pondahai/pico_keyboard_ime_terminal/hardware/v2_1/v2_1.kicad_sch

## KiCad design hardware/v2_1/v2_1.kicad_sch (2025-11-12)

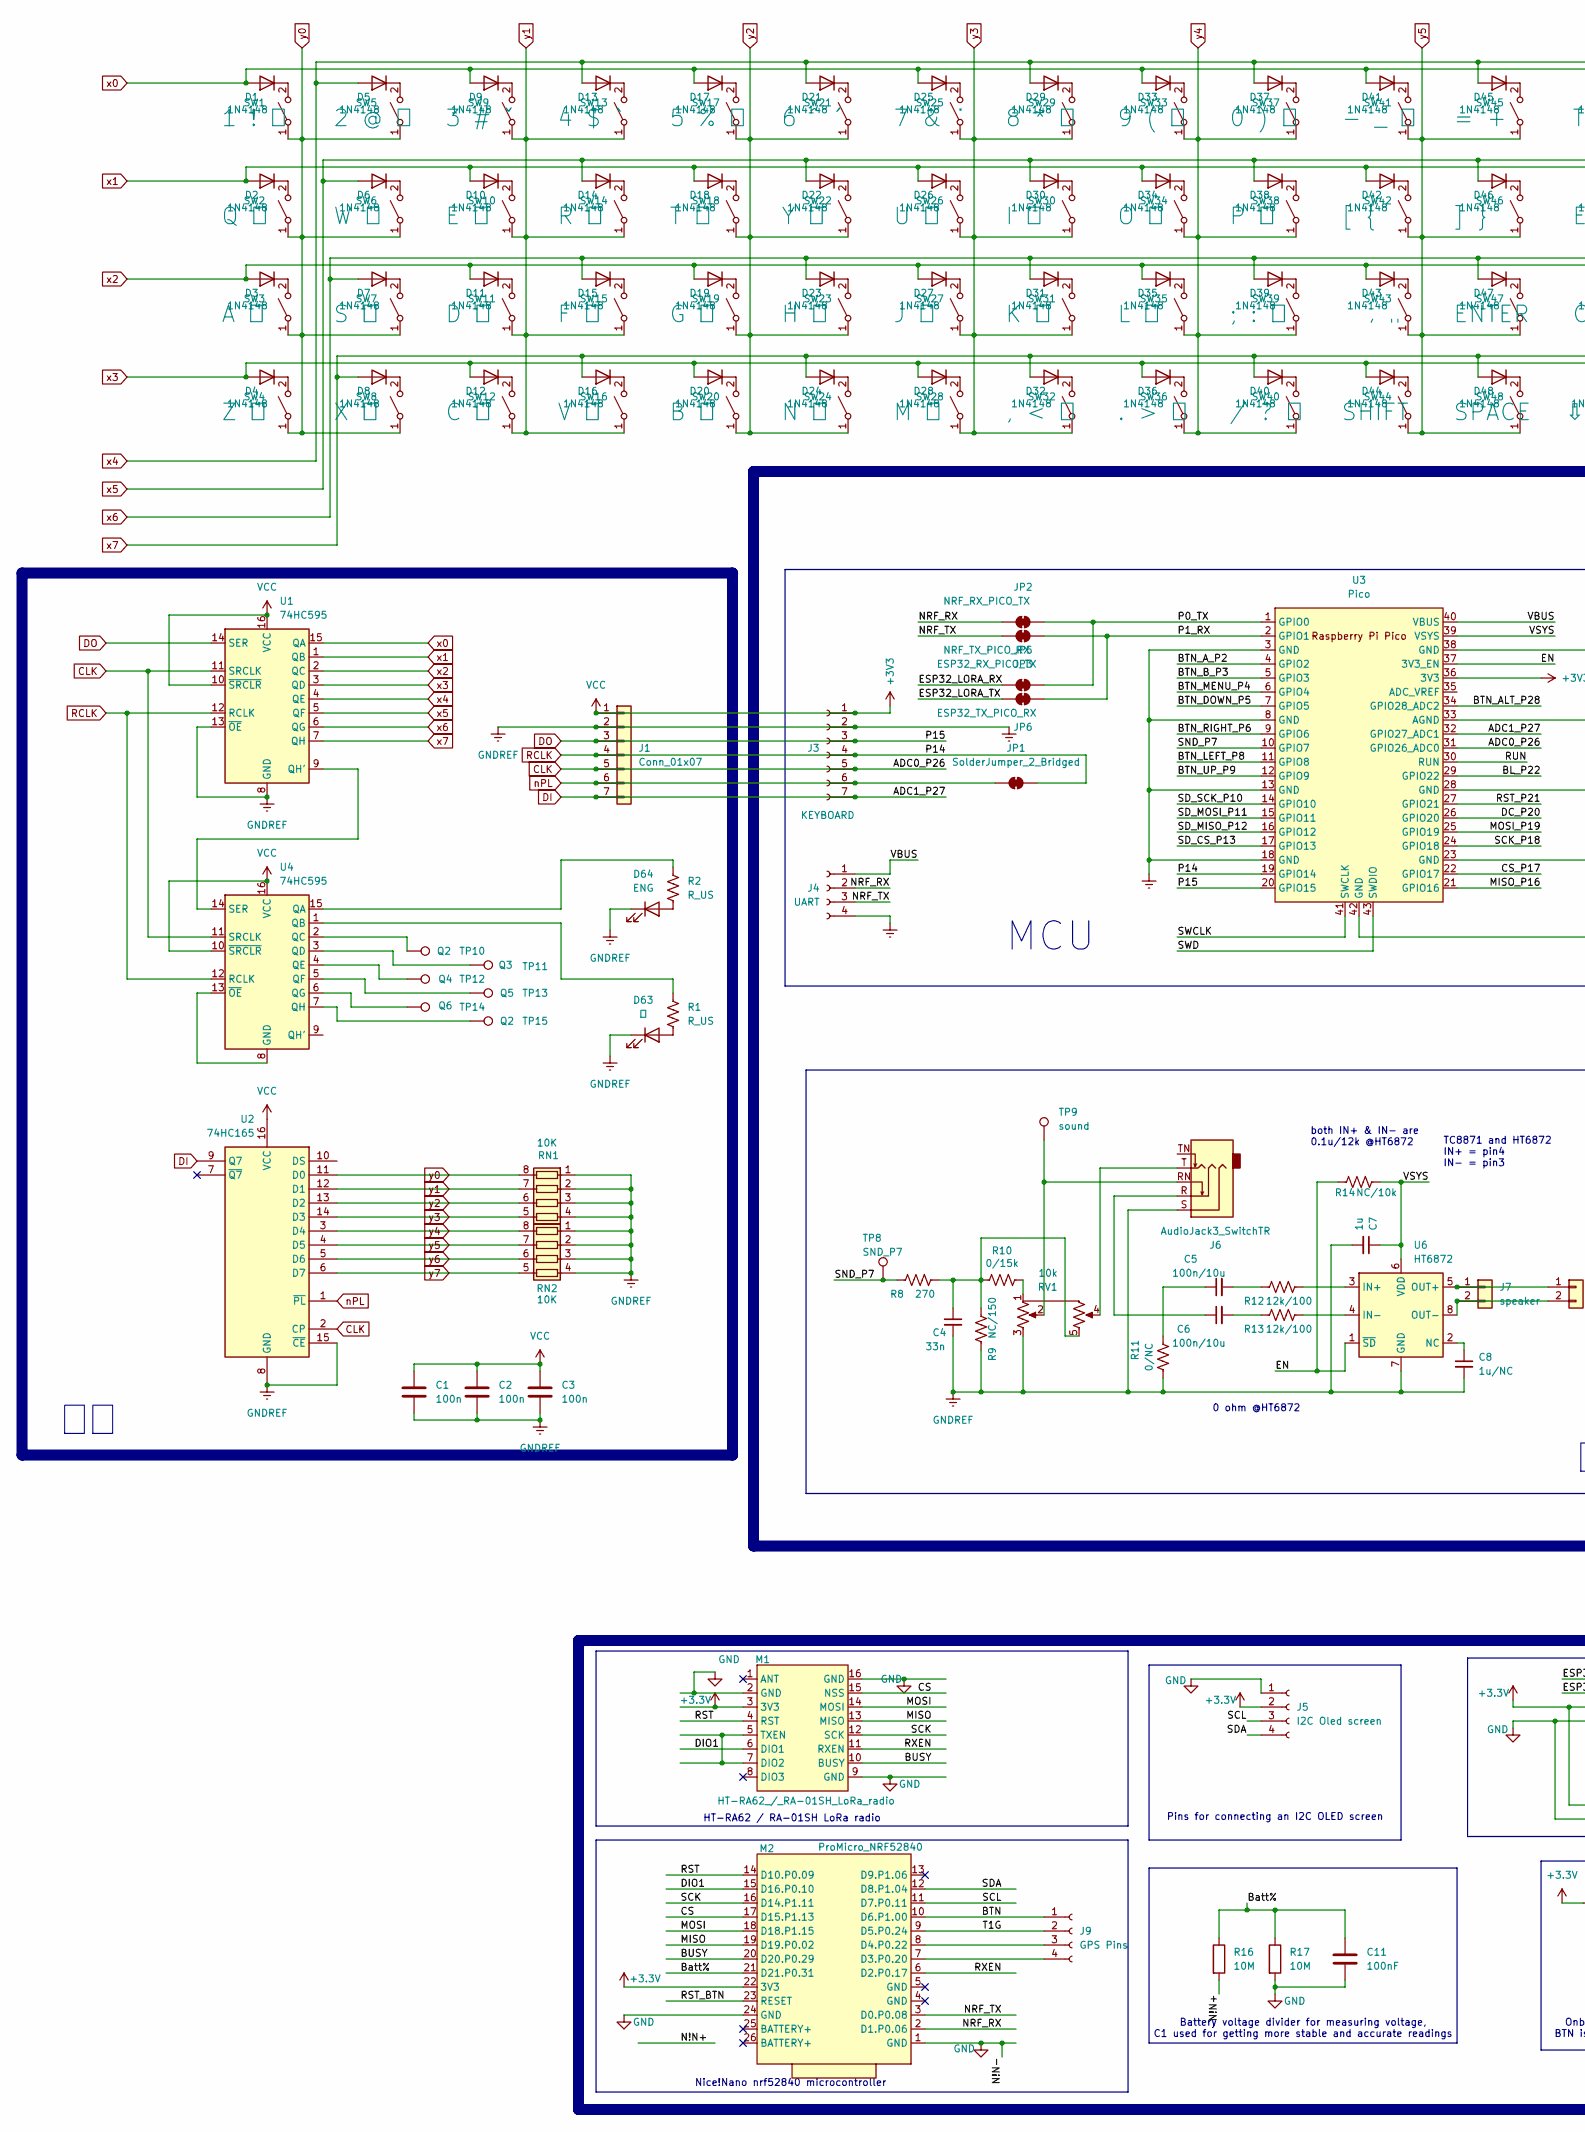
[picture p13: schematic v2_1.kicad_sch, part in row 1, column 1]

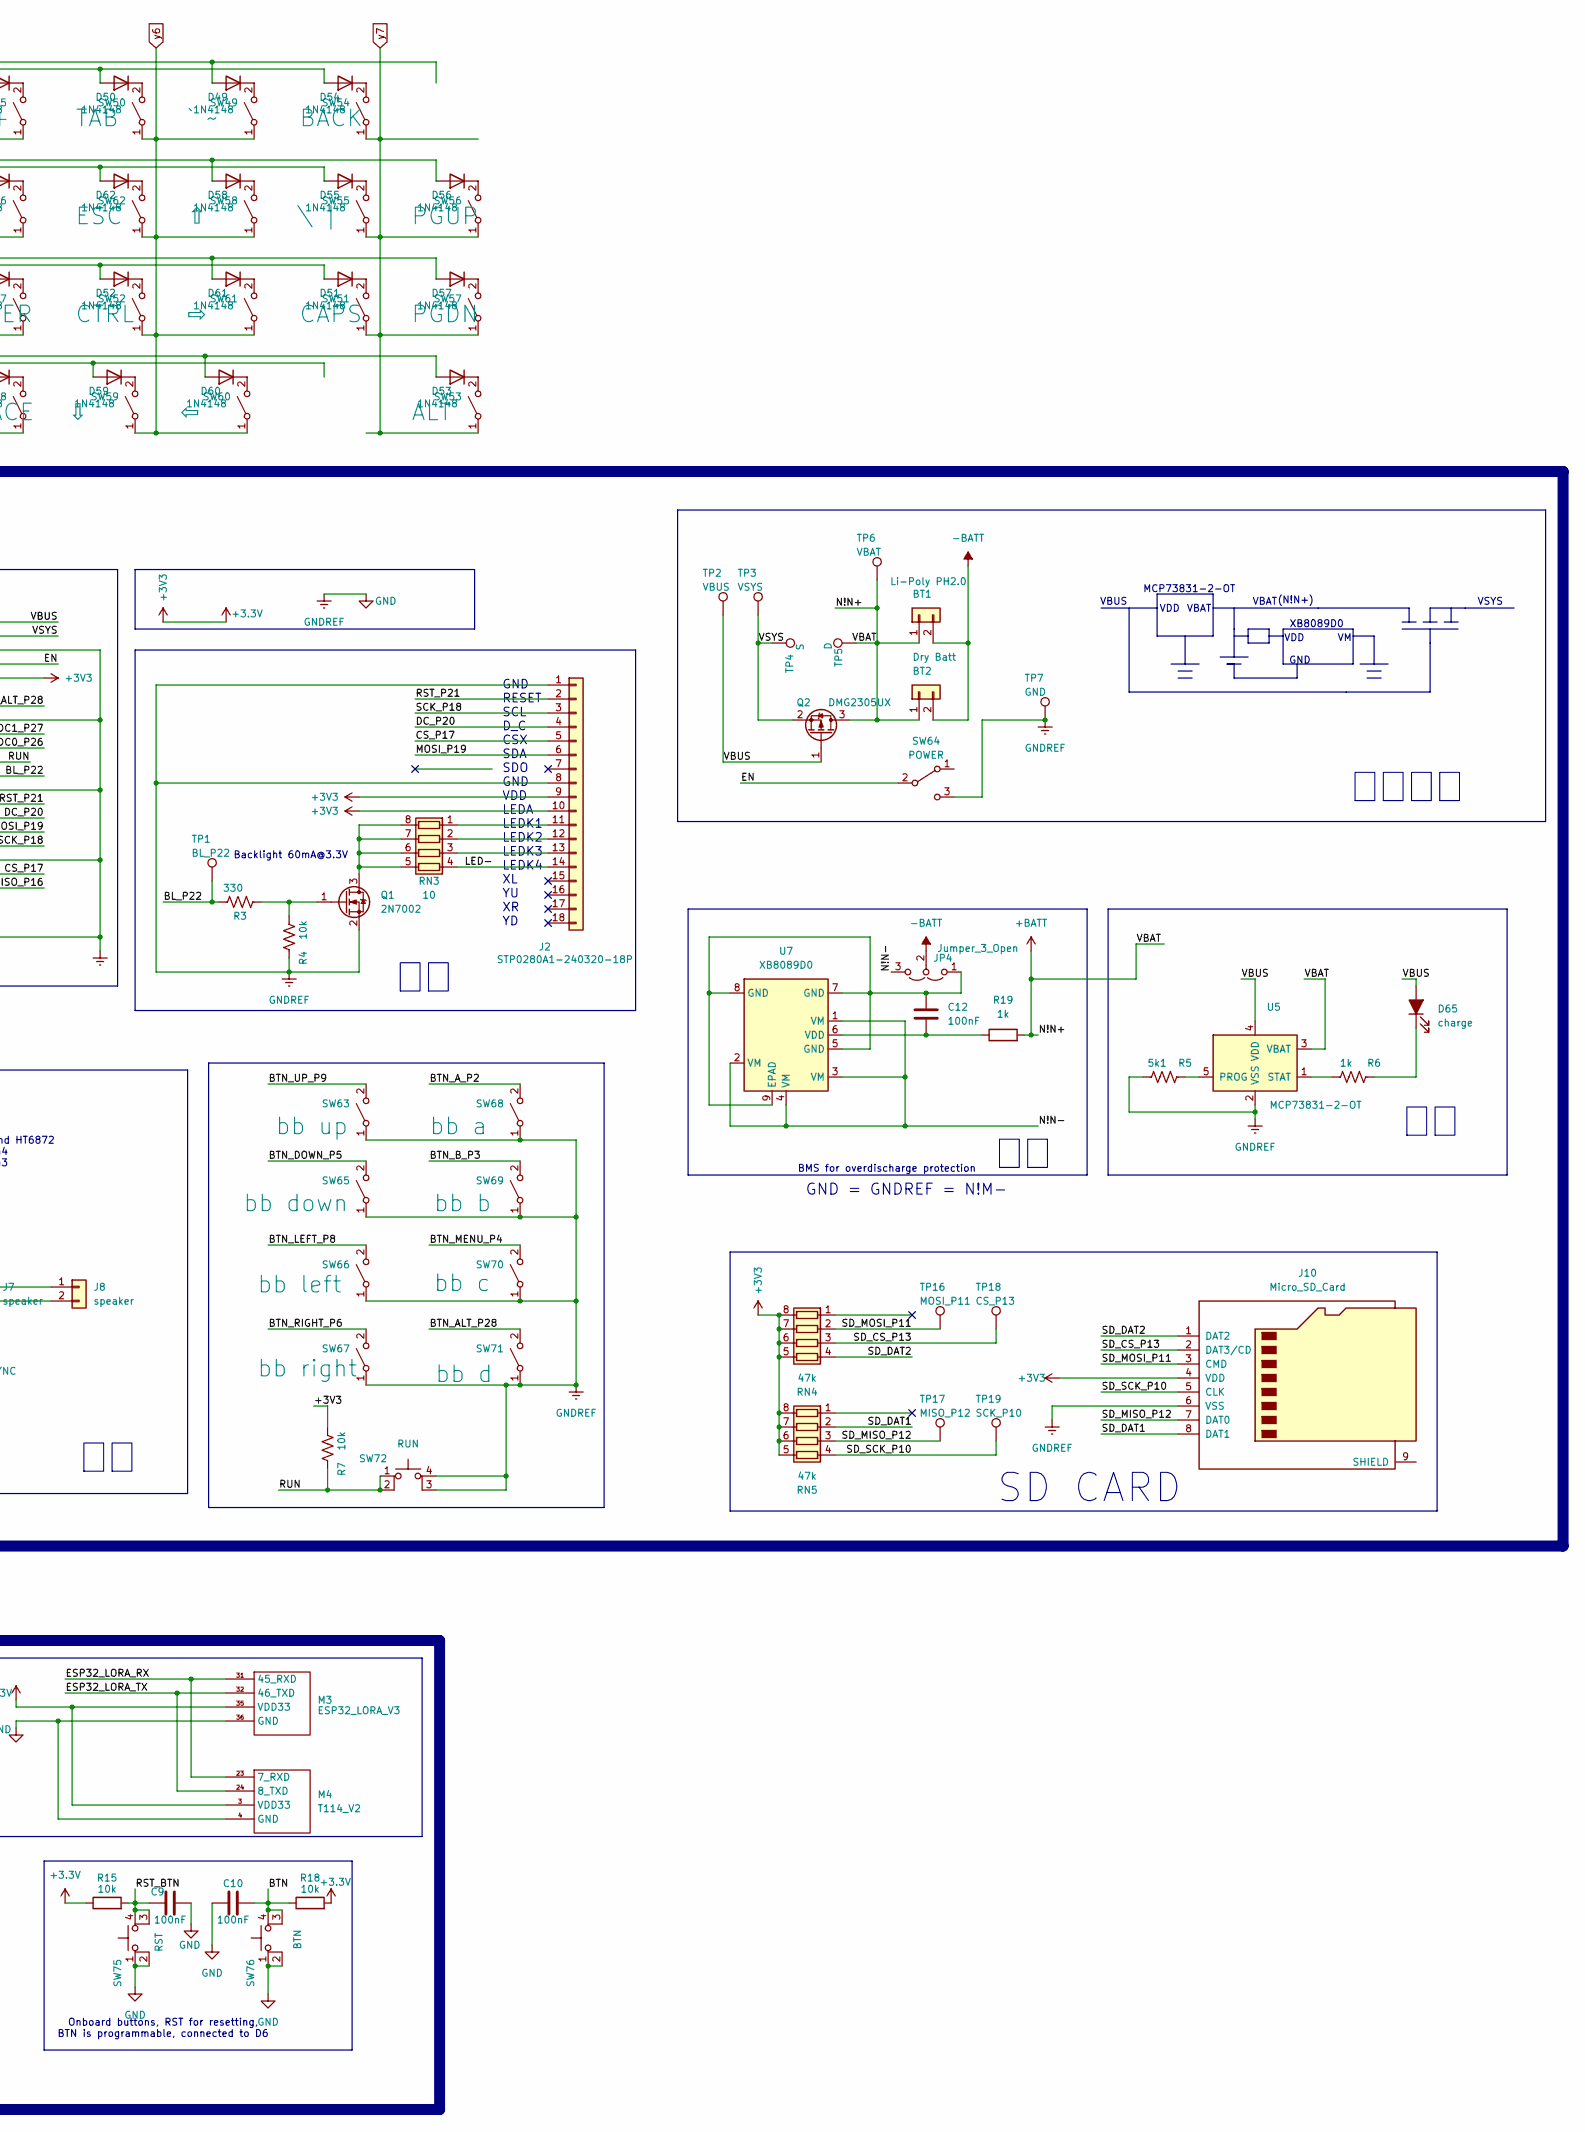
[picture p14: schematic v2_1.kicad_sch, part in row 1, column 2]

Parts:
BT1: Li-Poly PH2.0; JST_PH_B2B-PH-K_1x02_P2.00mm_Vertical
BT2: Dry Batt; BatteryHolder_Keystone_2479_3xAAA
C1, C2, C3: 100n; C_0805_2012Metric_Pad1.18x1.45mm_HandSolder
C4: 33n; C_0805_2012Metric_Pad1.18x1.45mm_HandSolder
C5, C6: 100n/10u; C_0805_2012Metric_Pad1.18x1.45mm_HandSolder
C7: 1u; C_0805_2012Metric_Pad1.18x1.45mm_HandSolder
C8: 1u/NC; C_0805_2012Metric_Pad1.18x1.45mm_HandSolder
C9, C10, C11: 100nF; C_0805_2012Metric_Pad1.18x1.45mm_HandSolder
C12: 100nF; C_1206_3216Metric_Pad1.33x1.80mm_HandSolder
D1, D2, D3, D4, D5, D6, D7, D8, D9, D10, D11, D12, D13, D14, D15, D16, D17, D18, D19, D20, D21, D22, D23, D24, D25, D26, D27, D28, D29, D30, D31, D32, D33, D34, D35, D36, D37, D38, D39, D40, D41, D42, D43, D44, D45, D46, D47, D48, D49, D50, D51, D52, D53, D54, D55, D56, D57, D58, D59, D60, D61, D62: 1N4148; D_0805_JUMPER
D63: ㄅ; LED_D3.0mm_Clear
D64: ENG; LED_D3.0mm_Clear
D65: charge; LED_0805_2012Metric_Pad1.15x1.40mm_HandSolder
J1: Conn_01x07; PinHeader_1x07_P2.54mm_Horizontal
J2: STP0280A1-240320-18P; STP0280A1-240320
J3: KEYBOARD; PinSocket_1x07_P2.54mm_Horizontal
J4: UART; PinSocket_1x04_P2.54mm_Horizontal
J5: I2C Oled screen; PinHeader_1x04_P2.54mm_Vertical
J6: AudioJack3_SwitchTR; audiojack-3.5mm-5p
J7: speaker; SolderWire-0.1sqmm_1x02_P3.6mm_D0.4mm_OD1mm
J8: speaker; Hirose_DF13-02P-1.25DSA_1x02_P1.25mm_Vertical
J9: GPS Pins; PinHeader_1x04_P2.54mm_Vertical
J10: Micro_SD_Card; sd-card
JP1: SolderJumper_2_Bridged; SolderJumper-2_P1.3mm_Bridged_Pad1.0x1.5mm
JP2: NRF_RX_PICO_TX; SolderJumper-2_P1.3mm_Bridged_Pad1.0x1.5mm
JP3: NRF_TX_PICO_RX; SolderJumper-2_P1.3mm_Bridged_Pad1.0x1.5mm
JP4: Jumper_3_Open; SolderJumper-3_P1.3mm_Open_RoundedPad1.0x1.5mm
JP5: ESP32_RX_PICO_TX; SolderJumper-2_P1.3mm_Bridged_Pad1.0x1.5mm
JP6: ESP32_TX_PICO_RX; SolderJumper-2_P1.3mm_Bridged_Pad1.0x1.5mm
M1: HT-RA62_/_RA-01SH_LoRa_radio; HT-RA62 RA-01SH LoRa radio
M2: ProMicro_NRF52840; ProMicro nrf52840
M3: ESP32_LORA_V3; LoRa-ESP32-V3
M4: T114_V2; T114
Q1: 2N7002; SOT-23_Handsoldering
Q2: DMG2305UX; SOT-23_Handsoldering
R1, R2: R_US; R_Axial_DIN0204_L3.6mm_D1.6mm_P7.62mm_Horizontal_0805
R3: 330; R_0805_2012Metric_Pad1.20x1.40mm_HandSolder
R4, R7, R15, R18: 10k; R_0805_2012Metric_Pad1.20x1.40mm_HandSolder
R5: 5k1; R_0805_2012Metric_Pad1.20x1.40mm_HandSolder
R6: 1k; R_0805_2012Metric_Pad1.20x1.40mm_HandSolder
R8: 270; R_0805_2012Metric_Pad1.20x1.40mm_HandSolder
R9: NC/150; R_0805_2012Metric_Pad1.20x1.40mm_HandSolder
R10: 0/15k; R_0805_2012Metric_Pad1.20x1.40mm_HandSolder
R11: 0/NC; R_0805_2012Metric_Pad1.20x1.40mm_HandSolder
R12, R13: 12k/100; R_0805_2012Metric_Pad1.20x1.40mm_HandSolder
R14: NC/10k; R_0805_2012Metric_Pad1.20x1.40mm_HandSolder
R16, R17: 10M; R_0805_2012Metric_Pad1.20x1.40mm_HandSolder
R19: 1k; R_1206_3216Metric_Pad1.30x1.75mm_HandSolder
RN1, RN2: 10K; R_Array_Convex_4x0603
RN3: 10; R_Array_Convex_4x0603
RN4, RN5: 47k; R_Array_Convex_4x0603
RV1: 10k; potentiometre disk 5pin
SW1: 1 ! ㄅ; SW_Push_1P1T_NO_CK_KSC7xxJ
SW2: Q ㄆ; SW_Push_1P1T_NO_CK_KSC7xxJ
SW3: A ㄇ; SW_Push_1P1T_NO_CK_KSC7xxJ
SW4: Z ㄈ; SW_Push_1P1T_NO_CK_KSC7xxJ
SW5: 2 @ ㄉ; SW_Push_1P1T_NO_CK_KSC7xxJ
SW6: W ㄊ; SW_Push_1P1T_NO_CK_KSC7xxJ
SW7: S ㄋ; SW_Push_1P1T_NO_CK_KSC7xxJ
SW8: X ㄌ; SW_Push_1P1T_NO_CK_KSC7xxJ
SW9: 3 # ˇ; SW_Push_1P1T_NO_CK_KSC7xxJ
SW10: E ㄍ; SW_Push_1P1T_NO_CK_KSC7xxJ
SW11: D ㄎ; SW_Push_1P1T_NO_CK_KSC7xxJ
SW12: C ㄏ; SW_Push_1P1T_NO_CK_KSC7xxJ
SW13: 4 $ ˋ; SW_Push_1P1T_NO_CK_KSC7xxJ
SW14: R ㄐ; SW_Push_1P1T_NO_CK_KSC7xxJ
SW15: F ㄑ; SW_Push_1P1T_NO_CK_KSC7xxJ
SW16: V ㄒ; SW_Push_1P1T_NO_CK_KSC7xxJ
SW17: 5 % ㄓ; SW_Push_1P1T_NO_CK_KSC7xxJ
SW18: T ㄔ; SW_Push_1P1T_NO_CK_KSC7xxJ
SW19: G ㄕ; SW_Push_1P1T_NO_CK_KSC7xxJ
SW20: B ㄖ; SW_Push_1P1T_NO_CK_KSC7xxJ
SW21: 6 ^ ˊ; SW_Push_1P1T_NO_CK_KSC7xxJ
SW22: Y ㄗ; SW_Push_1P1T_NO_CK_KSC7xxJ
SW23: H ㄘ; SW_Push_1P1T_NO_CK_KSC7xxJ
SW24: N ㄙ; SW_Push_1P1T_NO_CK_KSC7xxJ
SW25: 7 & ˙; SW_Push_1P1T_NO_CK_KSC7xxJ
SW26: U ㄧ; SW_Push_1P1T_NO_CK_KSC7xxJ
SW27: J ㄨ; SW_Push_1P1T_NO_CK_KSC7xxJ
SW28: M ㄩ; SW_Push_1P1T_NO_CK_KSC7xxJ
SW29: 8 * ㄚ; SW_Push_1P1T_NO_CK_KSC7xxJ
SW30: I ㄛ; SW_Push_1P1T_NO_CK_KSC7xxJ
SW31: K ㄜ; SW_Push_1P1T_NO_CK_KSC7xxJ
SW32: , < ㄝ; SW_Push_1P1T_NO_CK_KSC7xxJ
SW33: 9 ( ㄞ; SW_Push_1P1T_NO_CK_KSC7xxJ
SW34: O ㄟ; SW_Push_1P1T_NO_CK_KSC7xxJ
SW35: L ㄠ; SW_Push_1P1T_NO_CK_KSC7xxJ
SW36: . > ㄡ; SW_Push_1P1T_NO_CK_KSC7xxJ
SW37: 0 ) ㄢ; SW_Push_1P1T_NO_CK_KSC7xxJ
SW38: P ㄣ; SW_Push_1P1T_NO_CK_KSC7xxJ
SW39: ; : ㄤ; SW_Push_1P1T_NO_CK_KSC7xxJ
SW40: / ? ㄥ; SW_Push_1P1T_NO_CK_KSC7xxJ
SW41: - _ ㄦ; SW_Push_1P1T_NO_CK_KSC7xxJ
SW42: [ {; SW_Push_1P1T_NO_CK_KSC7xxJ
SW43: ' "; SW_Push_1P1T_NO_CK_KSC7xxJ
SW44: SHIFT; SW_Push_1P1T_NO_CK_KSC7xxJ
SW45: = +; SW_Push_1P1T_NO_CK_KSC7xxJ
SW46: ] }; SW_Push_1P1T_NO_CK_KSC7xxJ
SW47: ENTER; SW_Push_1P1T_NO_CK_KSC7xxJ
SW48: SPACE; SW_Push_1P1T_NO_CK_KSC7xxJ
SW49: ` ~; SW_Push_1P1T_NO_CK_KSC7xxJ
SW50: TAB; SW_Push_1P1T_NO_CK_KSC7xxJ
SW51: CAPS; SW_Push_1P1T_NO_CK_KSC7xxJ
SW52: CTRL; SW_Push_1P1T_NO_CK_KSC7xxJ
SW53: ALT; SW_Push_1P1T_NO_CK_KSC7xxJ
SW54: BACK; SW_Push_1P1T_NO_CK_KSC7xxJ
SW55: \ |; SW_Push_1P1T_NO_CK_KSC7xxJ
SW56: PGUP; SW_Push_1P1T_NO_CK_KSC7xxJ
SW57: PGDN; SW_Push_1P1T_NO_CK_KSC7xxJ
SW58: ⇧; SW_Push_1P1T_NO_CK_KSC7xxJ
SW59: ⇩; SW_Push_1P1T_NO_CK_KSC7xxJ
SW60: ⇦; SW_Push_1P1T_NO_CK_KSC7xxJ
SW61: ⇨; SW_Push_1P1T_NO_CK_KSC7xxJ
SW62: ESC; SW_Push_1P1T_NO_CK_KSC7xxJ
SW63: bb up; SW_Push_1P1T_NO_CK_KSC7xxJ
SW64: POWER; SW_CuK_JS202011AQN_DPDT_Angled
SW65: bb down; SW_Push_1P1T_NO_CK_KSC7xxJ
SW66: bb left; SW_Push_1P1T_NO_CK_KSC7xxJ
SW67: bb right; SW_Push_1P1T_NO_CK_KSC7xxJ
SW68: bb a; SW_Push_1P1T_NO_CK_KSC7xxJ
SW69: bb b; SW_Push_1P1T_NO_CK_KSC7xxJ
SW70: bb c; SW_Push_1P1T_NO_CK_KSC7xxJ
SW71: bb d; SW_Push_1P1T_NO_CK_KSC7xxJ
SW72: RUN; skrp
SW75: RST; skrp
SW76: BTN; skrp
TP1: BL_P22; TestPoint_Pad_D1.5mm
TP2: VBUS; TestPoint_Pad_D1.5mm
TP3: VSYS; TestPoint_Pad_D1.5mm
TP4: S; TestPoint_Pad_D1.5mm
TP5: D; TestPoint_Pad_D1.5mm
TP6: VBAT; TestPoint_THTPad_5.0x5.0mm_Drill2.0mm
TP7: GND; TestPoint_THTPad_5.0x5.0mm_Drill2.0mm
TP8: SND_P7; TestPoint_Pad_D1.5mm
TP9: sound; TestPoint_Pad_D1.5mm
TP10, TP15: Q2; TestPoint_Pad_D1.5mm
TP11: Q3; TestPoint_Pad_D1.5mm
TP12: Q4; TestPoint_Pad_D1.5mm
TP13: Q5; TestPoint_Pad_D1.5mm
TP14: Q6; TestPoint_Pad_D1.5mm
TP16: MOSI_P11; TestPoint_Pad_D1.5mm
TP17: MISO_P12; TestPoint_Pad_D1.5mm
TP18: CS_P13; TestPoint_Pad_D1.5mm
TP19: SCK_P10; TestPoint_Pad_D1.5mm
U1, U4: 74HC595; SOIC-16_3.9x9.9mm_P1.27mm
U2: 74HC165; SOIC-16_3.9x9.9mm_P1.27mm
U3: Pico; RaspberryPi_Pico_W_SMD_HandSolder
U5: MCP73831-2-OT; SOT-23-5
U6: HT6872; SOIC-8_3.9x4.9mm_P1.27mm
U7: XB8089D0; SOIC-8-1EP_3.9x4.9mm_P1.27mm_EP2.41x3.3mm

Connections:
+3.3V: C1.1, C2.1, C3.1, J1.1, J2.9, J2.10, J3.1, J5.2, J10.4 (VDD), M1.3 (3V3), M2.22 (3V3), M3.35 (VDD33), M4.3 (VDD33), R15.1, R18.2, RN4.5 (R4.2), RN4.6 (R3.2), RN4.7 (R2.2), RN4.8 (R1.2), RN5.5 (R4.2), RN5.6 (R3.2), RN5.7 (R2.2), RN5.8 (R1.2), U1.10 (~SRCLR), U1.16 (VCC), U2.16 (VCC), U3.36 (3V3), U4.10 (~SRCLR), U4.16 (VCC)
+3V3: R7.2
+BATT: BT1.1, BT2.1, Q2.3 (D), R16.2, R19.2, TP5.1, TP6.1, U5.3 (VBAT)
-BATT: BT1.2, BT2.2, JP4.2 (C)
BL_P22: R3.2, TP1.1, U3.29 (GPIO22)
BTN: C10.2, J9.1, M2.10 (D6.P1.00), R18.1, SW76.3 (K), SW76.4 (A)
BTN_ALT_P28: SW71.2 (B), U3.34 (GPIO28_ADC2)
BTN_A_P2: SW68.2 (B), U3.4 (GPIO2)
BTN_B_P3: SW69.2 (B), U3.5 (GPIO3)
BTN_DOWN_P5: SW65.2 (B), U3.7 (GPIO5)
BTN_LEFT_P8: SW66.2 (B), U3.11 (GPIO8)
BTN_MENU_P4: SW70.2 (B), U3.6 (GPIO4)
BTN_RIGHT_P6: SW67.2 (B), U3.9 (GPIO6)
BTN_UP_P9: SW63.2 (B), U3.12 (GPIO9)
BUSY: M1.10 (BUSY), M2.20 (D20.P0.29)
Batt%: C11.1, M2.21 (D21.P0.31), R16.1, R17.1
CLK: J1.5, J3.5, U1.11 (SRCLK), U2.2 (CP), U3.31 (GPIO26_ADC0), U4.11 (SRCLK)
CS: M1.15 (NSS), M2.17 (D15.P1.13)
CS_P17: J2.5, U3.22 (GPIO17)
DC_P20: J2.4, U3.26 (GPIO20)
DI: J1.7, J3.7, U2.9 (Q7), U3.32 (GPIO27_ADC1)
DIO1: M1.6 (DIO1), M2.15 (D16.P0.10)
DO: J1.3, J3.3, U1.14 (SER), U3.20 (GPIO15)
EN: R14.1, SW64.2 (B), U3.37 (3V3_EN), U6.1 (~SD)
ESP32_LORA_RX: JP5.2 (B), M3.31 (45_RXD), M4.23 (7_RXD)
ESP32_LORA_TX: JP6.2 (B), M3.32 (46_TXD), M4.24 (8_TXD)
GND: C1.2, C2.2, C3.2, C4.2, C7.2, C8.2, C9.2, C10.1, C11.2, D63.1 (K), D64.1 (K), J1.2, J2.1, J2.8, J3.2, J4.4, J5.1, J6.S, J10.6 (VSS), JP4.3 (B), M1.2 (GND), M1.9 (GND), M1.16 (GND), M2.1 (GND), M2.24 (GND), M3.36 (GND), M4.4 (GND), Q1.2 (S), R4.1, R5.2, R9.2, R11.1, R17.2, RN1.1 (R1.1), RN1.2 (R2.1), RN1.3 (R3.1), RN1.4 (R4.1), RN2.1 (R1.1), RN2.2 (R2.1), RN2.3 (R3.1), RN2.4 (R4.1), RV1.3, SW63.1 (A), SW64.3 (C), SW65.1 (A), SW66.1 (A), SW67.1 (A), SW68.1 (A), SW69.1 (A), SW70.1 (A), SW71.1 (A), SW72.3 (K), SW72.4 (A), SW75.1, SW75.2, SW76.1, SW76.2, TP7.1, U1.8 (GND), U1.13 (~OE), U2.8 (GND), U2.15 (~CE), U3.3 (GND), U3.8 (GND), U3.13 (GND), U3.18 (GND), U3.23 (GND), U3.28 (GND), U3.33 (AGND), U3.38 (GND), U3.42 (GND), U5.2 (VSS), U6.7 (GND), U7.1 (VM), U7.2 (VM), U7.3 (VM), U7.4 (VM)
LED-: J2.14, RN3.4 (R4.1)
MISO: M1.13 (MISO), M2.19 (D19.P0.02)
MISO_P16: U3.21 (GPIO16)
MOSI: M1.14 (MOSI), M2.18 (D18.P1.15)
MOSI_P19: J2.6, U3.25 (GPIO19)
NRF_RX: J4.2, JP2.2 (B), M2.2 (D1.P0.06)
NRF_TX: J4.3, JP3.2 (B), M2.3 (D0.P0.08)
unnamed: C4.1, R8.2, R9.1, R10.2, RV1.5 (3)
unnamed: C5.1, R11.2
unnamed: C5.2, R12.1
unnamed: C6.1, J6.R
unnamed: C6.2, R13.1
unnamed: C8.1, U6.2 (NC)
unnamed: C12.1, JP4.1 (A), U7.5 (GND), U7.7 (GND), U7.8 (GND), U7.9 (EPAD)
unnamed: C12.2, R19.1, U7.6 (VDD)
unnamed: D1.1 (K), SW1.2 (B)
unnamed: D2.1 (K), SW2.2 (B)
unnamed: D3.1 (K), SW3.2 (B)
unnamed: D4.1 (K), SW4.2 (B)
unnamed: D5.1 (K), SW5.2 (B)
unnamed: D6.1 (K), SW6.2 (B)
unnamed: D7.1 (K), SW7.2 (B)
unnamed: D8.1 (K), SW8.2 (B)
unnamed: D9.1 (K), SW9.2 (B)
unnamed: D10.1 (K), SW10.2 (B)
unnamed: D11.1 (K), SW11.2 (B)
unnamed: D12.1 (K), SW12.2 (B)
unnamed: D13.1 (K), SW13.2 (B)
unnamed: D14.1 (K), SW14.2 (B)
unnamed: D15.1 (K), SW15.2 (B)
unnamed: D16.1 (K), SW16.2 (B)
unnamed: D17.1 (K), SW17.2 (B)
unnamed: D18.1 (K), SW18.2 (B)
unnamed: D19.1 (K), SW19.2 (B)
unnamed: D20.1 (K), SW20.2 (B)
unnamed: D21.1 (K), SW21.2 (B)
unnamed: D22.1 (K), SW22.2 (B)
unnamed: D23.1 (K), SW23.2 (B)
unnamed: D24.1 (K), SW24.2 (B)
unnamed: D25.1 (K), SW25.2 (B)
unnamed: D26.1 (K), SW26.2 (B)
unnamed: D27.1 (K), SW27.2 (B)
unnamed: D28.1 (K), SW28.2 (B)
unnamed: D29.1 (K), SW29.2 (B)
unnamed: D30.1 (K), SW30.2 (B)
unnamed: D31.1 (K), SW31.2 (B)
unnamed: D32.1 (K), SW32.2 (B)
unnamed: D33.1 (K), SW33.2 (B)
unnamed: D34.1 (K), SW34.2 (B)
unnamed: D35.1 (K), SW35.2 (B)
unnamed: D36.1 (K), SW36.2 (B)
unnamed: D37.1 (K), SW37.2 (B)
unnamed: D38.1 (K), SW38.2 (B)
unnamed: D39.1 (K), SW39.2 (B)
unnamed: D40.1 (K), SW40.2 (B)
unnamed: D41.1 (K), SW41.2 (B)
unnamed: D42.1 (K), SW42.2 (B)
unnamed: D43.1 (K), SW43.2 (B)
unnamed: D44.1 (K), SW44.2 (B)
unnamed: D45.1 (K), SW45.2 (B)
unnamed: D46.1 (K), SW46.2 (B)
unnamed: D47.1 (K), SW47.2 (B)
unnamed: D48.1 (K), SW48.2 (B)
unnamed: D49.1 (K), SW49.2 (B)
unnamed: D50.1 (K), SW50.2 (B)
unnamed: D51.1 (K), SW51.2 (B)
unnamed: D52.1 (K), SW52.2 (B)
unnamed: D53.1 (K), SW53.2 (B)
unnamed: D54.1 (K), SW54.2 (B)
unnamed: D55.1 (K), SW55.2 (B)
unnamed: D56.1 (K), SW56.2 (B)
unnamed: D57.1 (K), SW57.2 (B)
unnamed: D58.1 (K), SW58.2 (B)
unnamed: D59.1 (K), SW59.2 (B)
unnamed: D60.1 (K), SW60.2 (B)
unnamed: D61.1 (K), SW61.2 (B)
unnamed: D62.1 (K), SW62.2 (B)
unnamed: D63.2 (A), R1.2
unnamed: D64.2 (A), R2.2
unnamed: D65.1 (K), R6.1
unnamed: J2.11, RN3.1 (R1.1)
unnamed: J2.12, RN3.2 (R2.1)
unnamed: J2.13, RN3.3 (R3.1)
unnamed: J6.RN, RV1.2, TP9.1
unnamed: J6.T, RV1.4 (2)
unnamed: J7.1, J8.1, U6.5 (OUT+)
unnamed: J7.2, J8.2, U6.8 (OUT-)
unnamed: J9.3, M2.8 (D4.P0.22)
unnamed: J9.4, M2.7 (D3.P0.20)
unnamed: M1.5 (TXEN), M1.7 (DIO2)
unnamed: Q1.1 (G), R3.1, R4.2
unnamed: Q1.3 (D), RN3.5 (R4.2), RN3.6 (R3.2), RN3.7 (R2.2), RN3.8 (R1.2)
unnamed: R1.1, U4.1 (QB)
unnamed: R2.1, U4.15 (QA)
unnamed: R5.1, U5.5 (PROG)
unnamed: R6.2, U5.1 (STAT)
unnamed: R10.1, RV1.1
unnamed: R12.2, U6.3 (IN+)
unnamed: R13.2, U6.4 (IN-)
unnamed: TP10.1, U4.2 (QC)
unnamed: TP11.1, U4.3 (QD)
unnamed: TP12.1, U4.4 (QE)
unnamed: TP13.1, U4.5 (QF)
unnamed: TP14.1, U4.6 (QG)
unnamed: TP15.1, U4.7 (QH)
unnamed: U1.9 (QH'), U4.14 (SER)
unnamed: U4.8 (GND), U4.13 (~OE)
P0_TX: JP2.1 (A), JP5.1 (A), U3.1 (GPIO0)
P1_RX: JP3.1 (A), JP6.1 (A), U3.2 (GPIO1)
RCLK: J1.4, J3.4, JP1.1 (A), U1.12 (RCLK), U3.19 (GPIO14), U4.12 (RCLK)
RST: M1.4 (RST), M2.14 (D10.P0.09)
RST_BTN: C9.1, M2.23 (RESET), R15.2, SW75.3 (K), SW75.4 (A)
RST_P21: J2.2, U3.27 (GPIO21)
RUN: R7.1, SW72.1, SW72.2, U3.30 (RUN)
RXEN: M1.11 (RXEN), M2.6 (D2.P0.17)
SCK: M1.12 (SCK), M2.16 (D14.P1.11)
SCK_P18: J2.3, U3.24 (GPIO18)
SCL: J5.3, M2.11 (D7.P0.11)
SDA: J5.4, M2.12 (D8.P1.04)
SD_CS_P13: J10.2 (DAT3/CD), RN4.3 (R3.1), TP18.1, U3.17 (GPIO13)
SD_DAT1: J10.8 (DAT1), RN5.2 (R2.1)
SD_DAT2: J10.1 (DAT2), RN4.4 (R4.1)
SD_MISO_P12: J10.7 (DAT0), RN5.3 (R3.1), TP17.1, U3.16 (GPIO12)
SD_MOSI_P11: J10.3 (CMD), RN4.2 (R2.1), TP16.1, U3.15 (GPIO11)
SD_SCK_P10: J10.5 (CLK), RN5.4 (R4.1), TP19.1, U3.14 (GPIO10)
SND_P7: R8.1, TP8.1, U3.10 (GPIO7)
SWCLK: U3.41 (SWCLK)
SWD: U3.43 (SWDIO)
T1G: J9.2, M2.9 (D5.P0.24)
VBUS: D65.2 (A), J4.1, Q2.1 (G), TP2.1, U3.40 (VBUS), U5.4 (VDD)
VSYS: C7.1, Q2.2 (S), R14.2, TP3.1, TP4.1, U3.39 (VSYS), U6.6 (VDD)
nPL: J1.6, J3.6, JP1.2 (B), U2.1 (~PL)
x0: D1.2 (A), D9.2 (A), D17.2 (A), D25.2 (A), D33.2 (A), D41.2 (A), D50.2 (A), D54.2 (A), U1.15 (QA)
x1: D2.2 (A), D10.2 (A), D18.2 (A), D26.2 (A), D34.2 (A), D42.2 (A), D55.2 (A), D62.2 (A), U1.1 (QB)
x2: D3.2 (A), D11.2 (A), D19.2 (A), D27.2 (A), D35.2 (A), D43.2 (A), D51.2 (A), D52.2 (A), U1.2 (QC)
x3: D4.2 (A), D12.2 (A), D20.2 (A), D28.2 (A), D36.2 (A), D44.2 (A), D59.2 (A), U1.3 (QD)
x4: D5.2 (A), D13.2 (A), D21.2 (A), D29.2 (A), D37.2 (A), D45.2 (A), D49.2 (A), U1.4 (QE)
x5: D6.2 (A), D14.2 (A), D22.2 (A), D30.2 (A), D38.2 (A), D46.2 (A), D56.2 (A), D58.2 (A), U1.5 (QF)
x6: D7.2 (A), D15.2 (A), D23.2 (A), D31.2 (A), D39.2 (A), D47.2 (A), D57.2 (A), D61.2 (A), U1.6 (QG)
x7: D8.2 (A), D16.2 (A), D24.2 (A), D32.2 (A), D40.2 (A), D48.2 (A), D53.2 (A), D60.2 (A), U1.7 (QH)
y0: RN1.8 (R1.2), SW1.1 (A), SW2.1 (A), SW3.1 (A), SW4.1 (A), SW5.1 (A), SW6.1 (A), SW7.1 (A), SW8.1 (A), U2.11 (D0)
y1: RN1.7 (R2.2), SW9.1 (A), SW10.1 (A), SW11.1 (A), SW12.1 (A), SW13.1 (A), SW14.1 (A), SW15.1 (A), SW16.1 (A), U2.12 (D1)
y2: RN1.6 (R3.2), SW17.1 (A), SW18.1 (A), SW19.1 (A), SW20.1 (A), SW21.1 (A), SW22.1 (A), SW23.1 (A), SW24.1 (A), U2.13 (D2)
y3: RN1.5 (R4.2), SW25.1 (A), SW26.1 (A), SW27.1 (A), SW28.1 (A), SW29.1 (A), SW30.1 (A), SW31.1 (A), SW32.1 (A), U2.14 (D3)
y4: RN2.8 (R1.2), SW33.1 (A), SW34.1 (A), SW35.1 (A), SW36.1 (A), SW37.1 (A), SW38.1 (A), SW39.1 (A), SW40.1 (A), U2.3 (D4)
y5: RN2.7 (R2.2), SW41.1 (A), SW42.1 (A), SW43.1 (A), SW44.1 (A), SW45.1 (A), SW46.1 (A), SW47.1 (A), SW48.1 (A), U2.4 (D5)
y6: RN2.6 (R3.2), SW49.1 (A), SW50.1 (A), SW52.1 (A), SW58.1 (A), SW59.1 (A), SW60.1 (A), SW61.1 (A), SW62.1 (A), U2.5 (D6)
y7: RN2.5 (R4.2), SW51.1 (A), SW53.1 (A), SW54.1 (A), SW55.1 (A), SW56.1 (A), SW57.1 (A), U2.6 (D7)

Notes on the sheet:
VDD
0 ohm @HT6872
VSYS
(N!N+)
SD CARD
GND = GNDREF = N!M-
HT-RA62 / RA-01SH LoRa radio
both IN+ & IN- are 0.1u/12k @HT6872
GND RESET SCL D_C CSX SDA SDO GND VDD LEDA LEDK1 LEDK2 LEDK3 LEDK4 XL YU XR YD
Pins for connecting an I2C OLED screen
MCP73831-2-OT
MCU
VBAT
Onboard buttons, RST for resetting, BTN is programmable, connected to D6
XB8089D0
Nice!Nano nrf52840 microcontroller
Backlight 60mA@3.3V
電源拓普
BMS for overdischarge protection
GND
TC8871 and HT6872 IN+ = pin4 IN- = pin3
VBUS
Battery voltage divider for measuring voltage, C1 used for getting more stable and accurate readings
